RBSC/SideSlotGotekAdapter/Pics/board.jpg

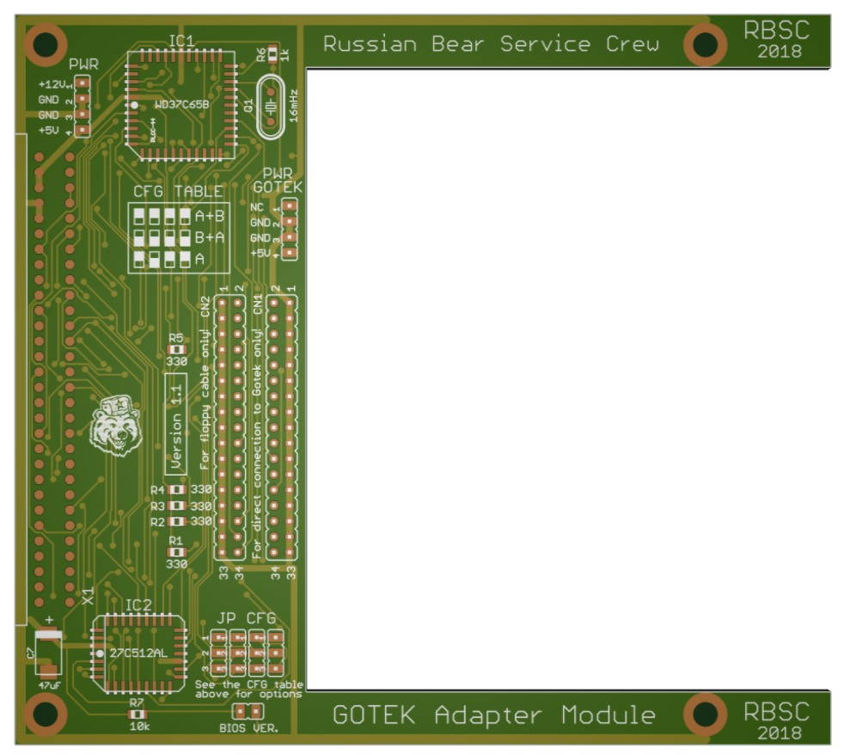
Pics/board.jpg
