RBSC/SideSlotGotekAdapter/Pics/floppy_connected2.jpg

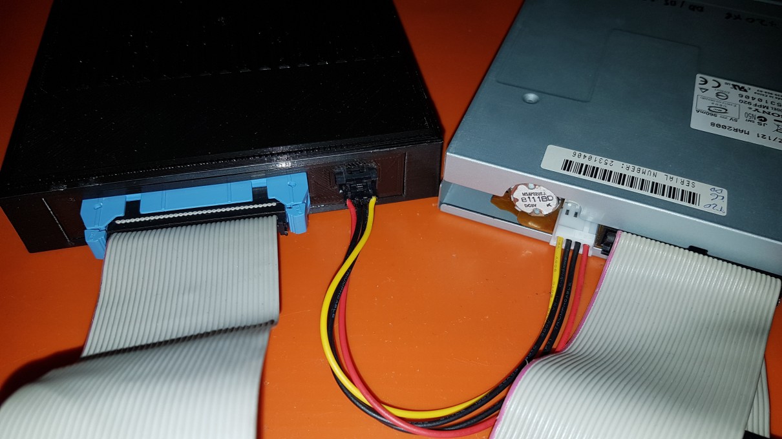
Pics/floppy_connected2.jpg
