RBSC/SideSlotGotekAdapter/Pics/gotek_in1.jpg

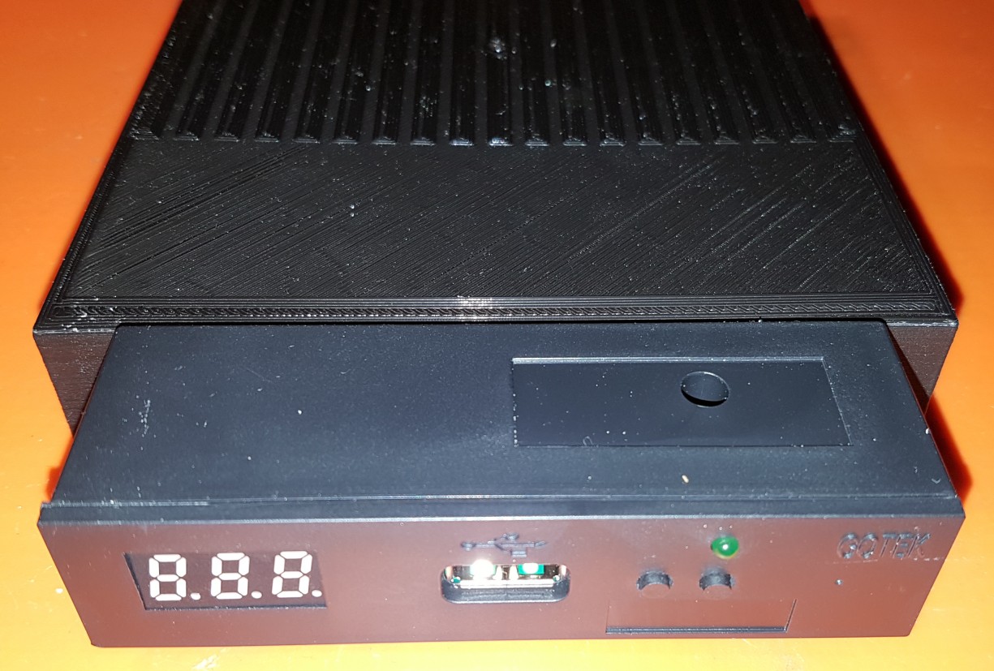
Pics/gotek_in1.jpg
