RBSC/SideSlotGotekAdapter/Pics/gotek_in2.jpg

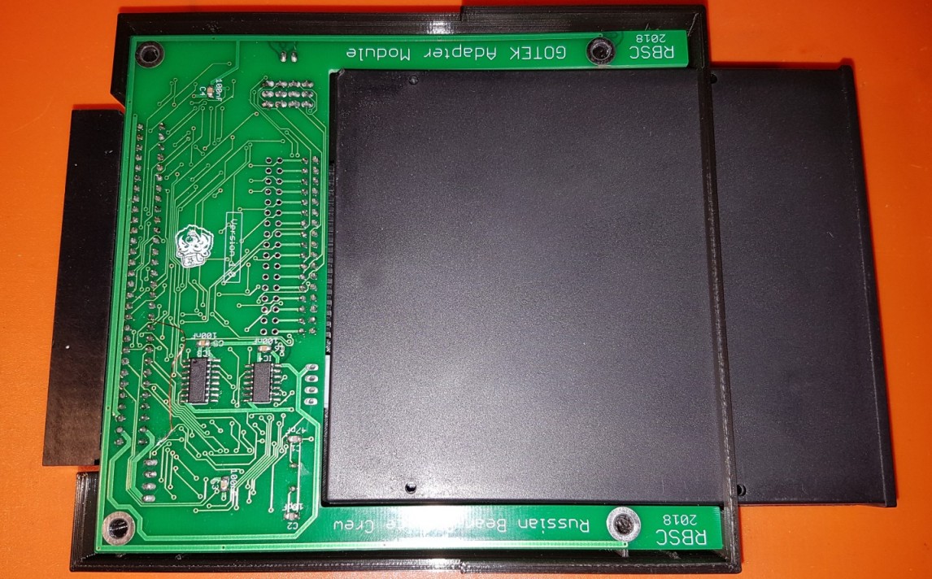
Pics/gotek_in2.jpg
