RBSC/SideSlotGotekAdapter/Pics/holders.jpg

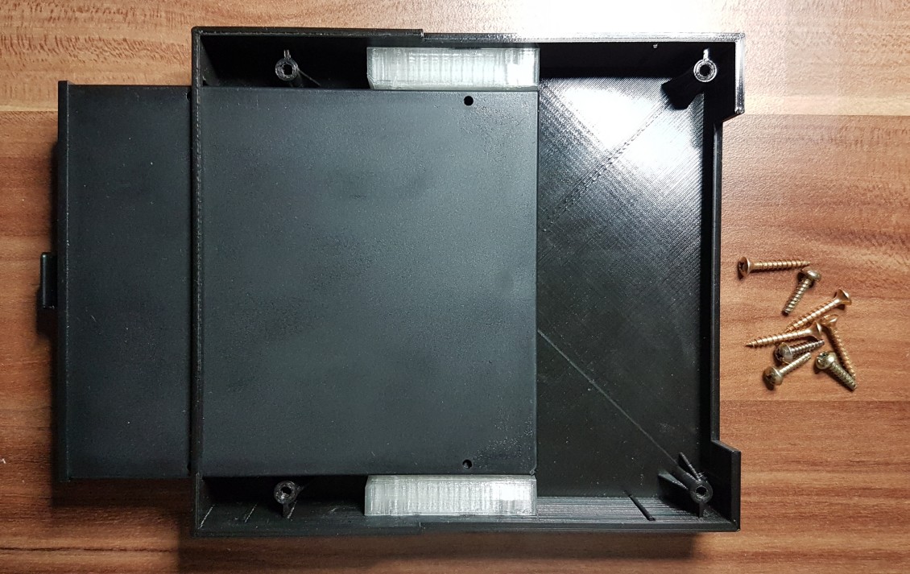
Pics/holders.jpg
