RBSC/SideSlotGotekAdapter/Pics/screws.jpg

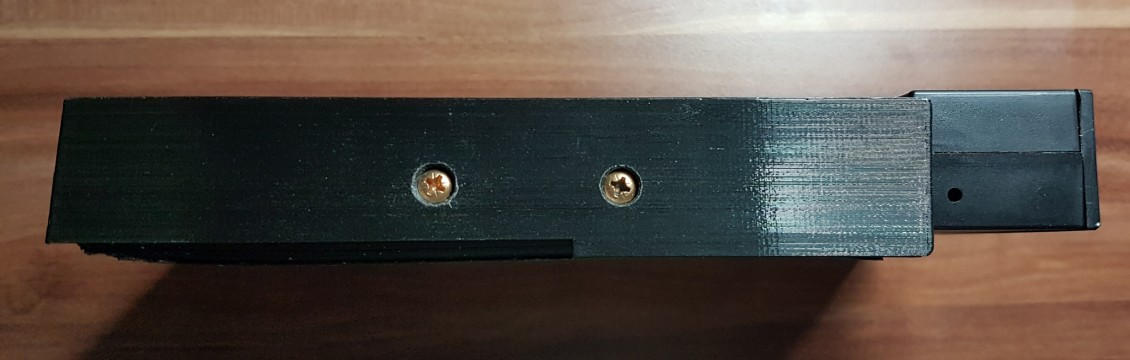
Pics/screws.jpg
